FITLab-Swansea/PV-Pix/CAD design/FabricOn Prototype/OPV_FLAT.SLDPRT

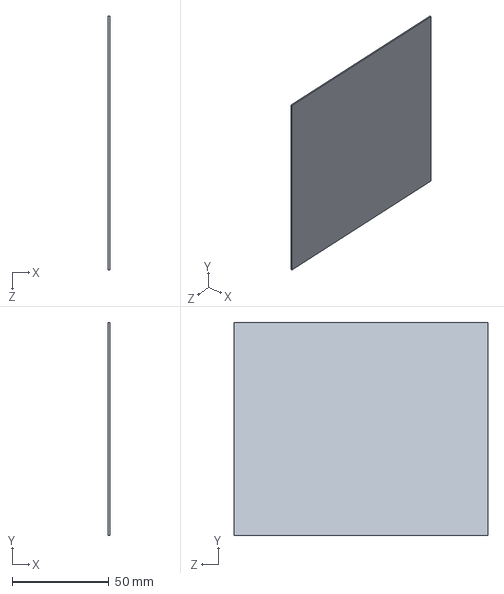
[picture p19: CAD file, 2021-02-02]
CAD design/FabricOn Prototype/OPV_FLAT.SLDPRT
0.85 x 110.0 x 131.1 mm
