FITLab-Swansea/PV-Pix/CAD design/Tilttile Prototype/Side_Frame.SLDPRT

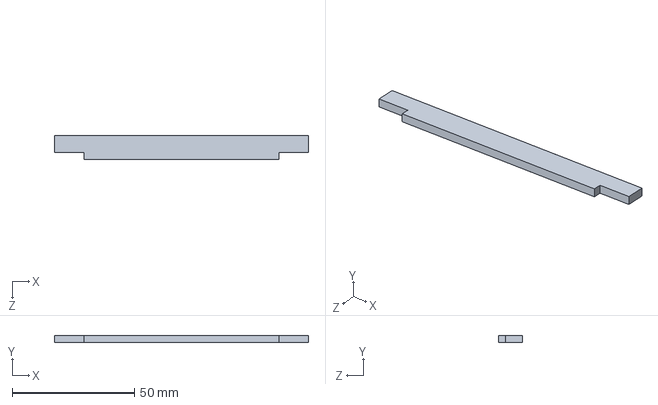
[picture p20: CAD file, 2021-02-02]
CAD design/Tilttile Prototype/Side_Frame.SLDPRT
104.0 x 3.00 x 10.0 mm
