FITLab-Swansea/PV-Pix/CAD design/Tilttile Prototype/Legs.SLDPRT

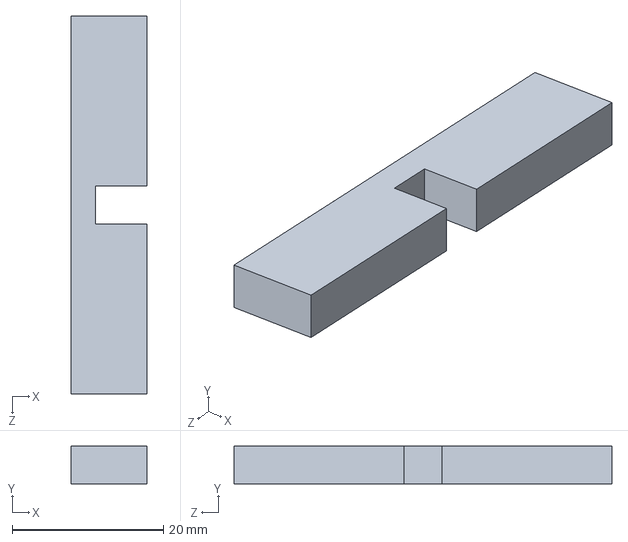
[picture p21: CAD file, 2021-02-02]
CAD design/Tilttile Prototype/Legs.SLDPRT
10.0 x 5.00 x 50.0 mm
