FITLab-Swansea/PV-Pix/CAD design/FabricOn Prototype/Hollow_Roller_Servo_Side.SLDPRT

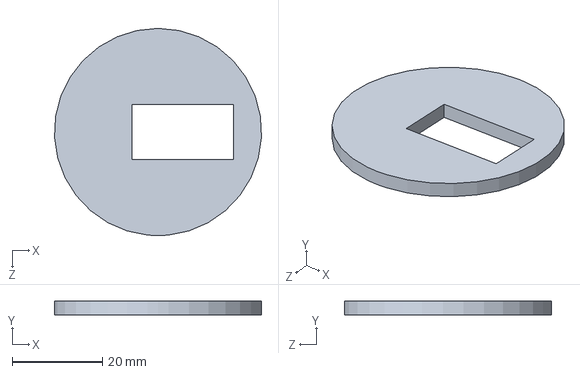
[picture p22: CAD file, 2021-02-02]
CAD design/FabricOn Prototype/Hollow_Roller_Servo_Side.SLDPRT
45.9 x 3.00 x 46.0 mm
