FITLab-Swansea/PV-Pix/CAD design/Tilttile Prototype/cover.SLDPRT

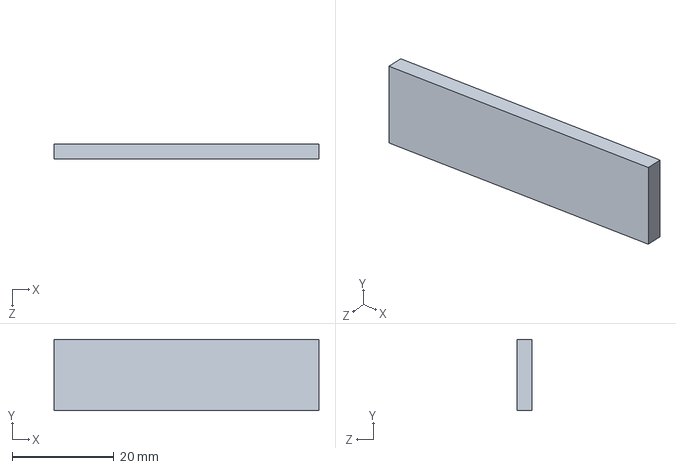
[picture p23: CAD file, 2021-02-02]
CAD design/Tilttile Prototype/cover.SLDPRT
52.0 x 14.0 x 3.00 mm
