FITLab-Swansea/PV-Pix/CAD design/FabricOn Prototype/Back_Plate.SLDPRT

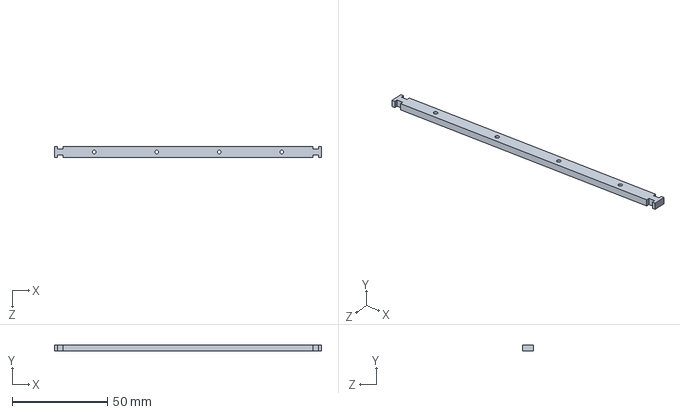
[picture p24: CAD file, 2021-02-02]
CAD design/FabricOn Prototype/Back_Plate.SLDPRT
140.0 x 3.00 x 6.00 mm
