FITLab-Swansea/PV-Pix/CAD design/Tilttile Prototype/Outer_Frame.SLDPRT

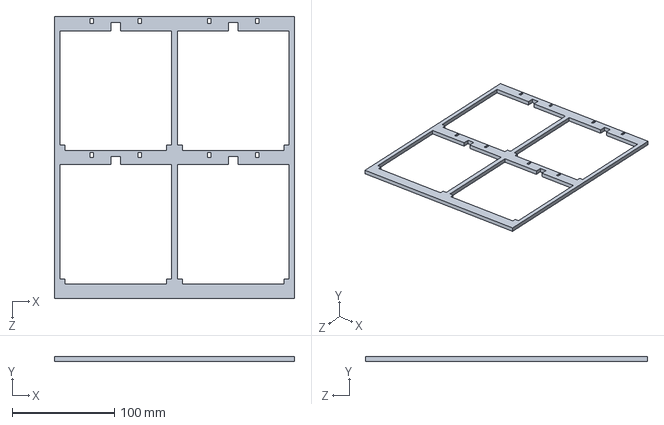
[picture p25: CAD file, 2021-02-02]
CAD design/Tilttile Prototype/Outer_Frame.SLDPRT
235.0 x 5.00 x 276.0 mm
