FITLab-Swansea/PV-Pix/CAD design/Tilttile Prototype/LeftMount.SLDPRT

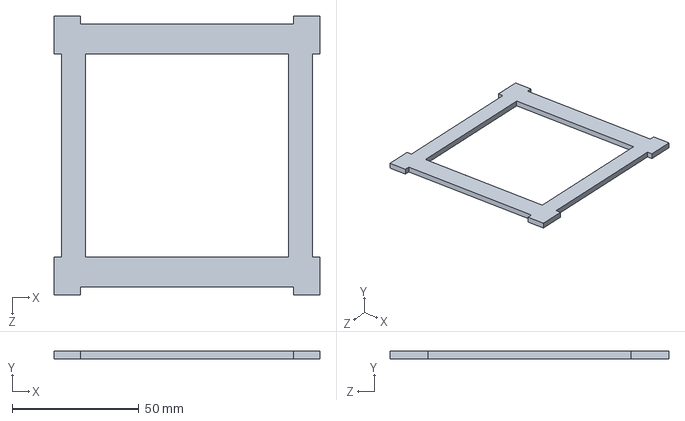
[picture p26: CAD file, 2021-02-02]
CAD design/Tilttile Prototype/LeftMount.SLDPRT
105.0 x 3.00 x 110.0 mm
